lizihan021/Marty-the-robot/pic/marty/5.JPG

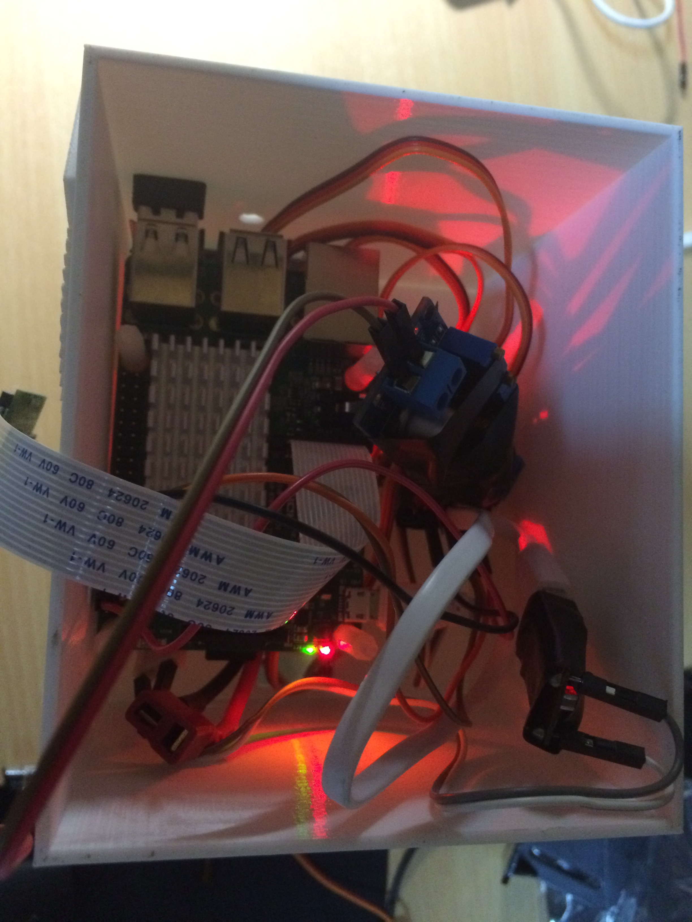
pic/marty/5.JPG
