lizihan021/Marty-the-robot/pic/marty/6.JPG

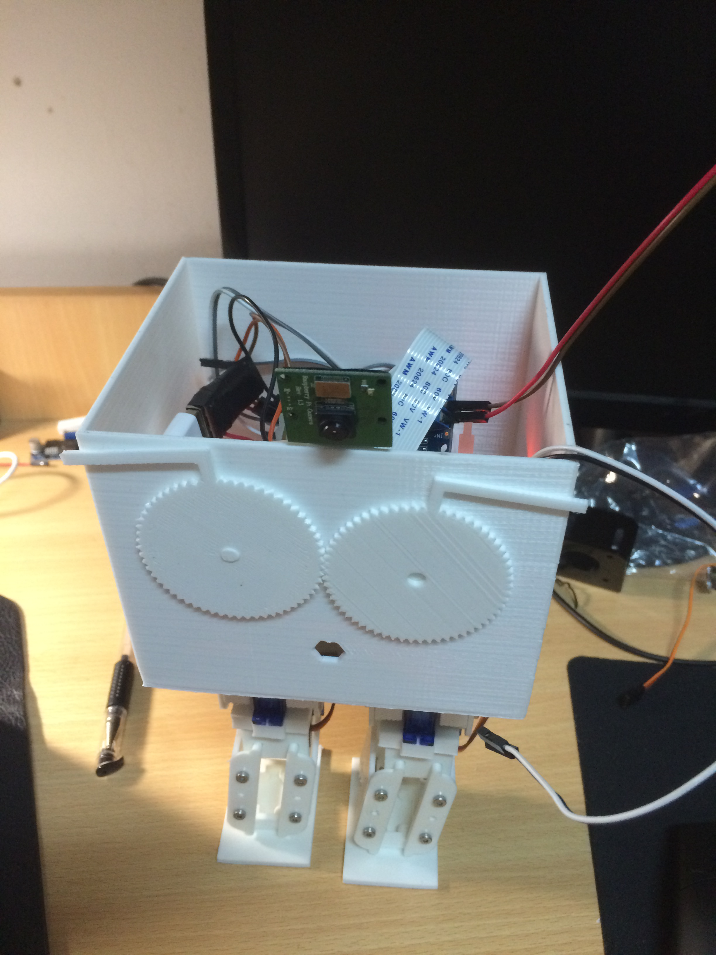
pic/marty/6.JPG
