lizihan021/Marty-the-robot/pic/marty/7.JPG

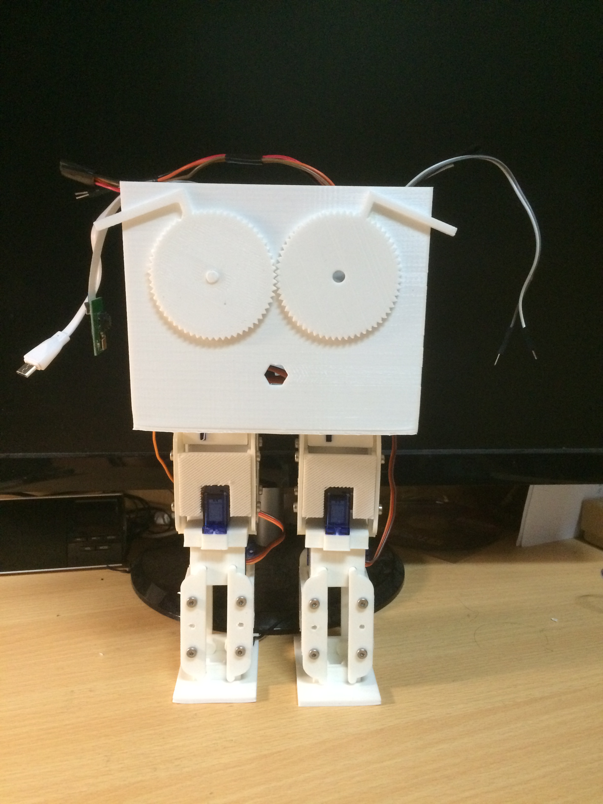
pic/marty/7.JPG
