lizihan021/Marty-the-robot/pic/marty/8.JPG

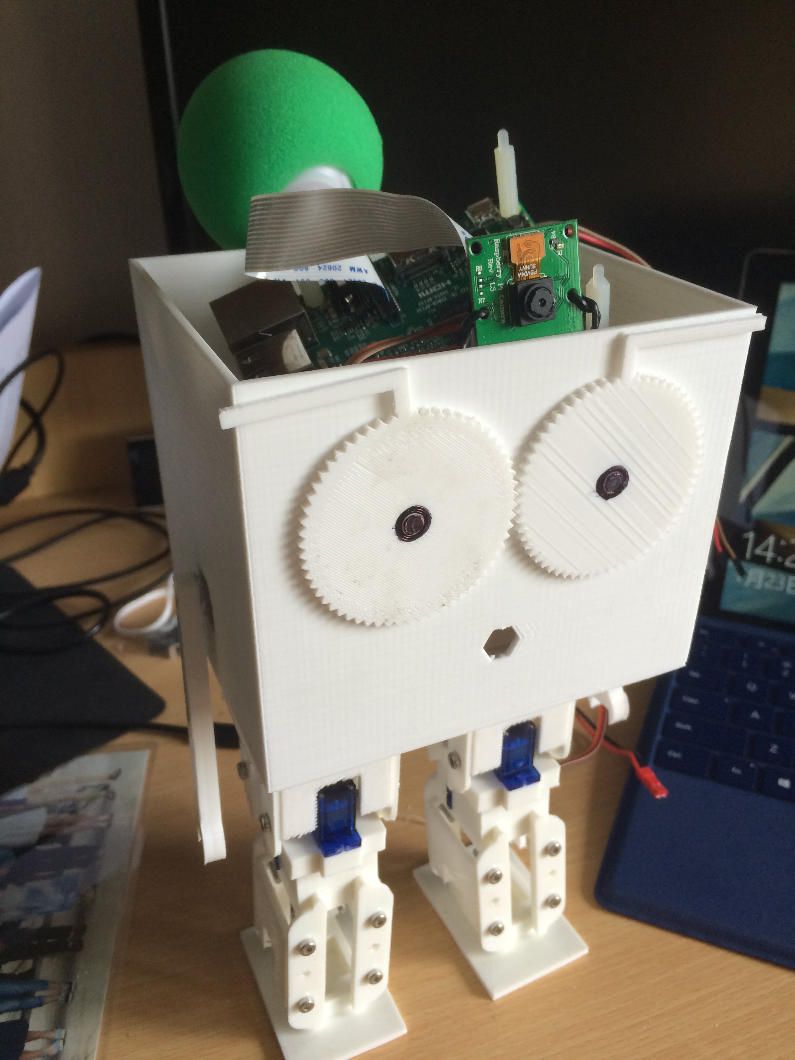
pic/marty/8.JPG
