lizihan021/Marty-the-robot/pic/marty/9.JPG

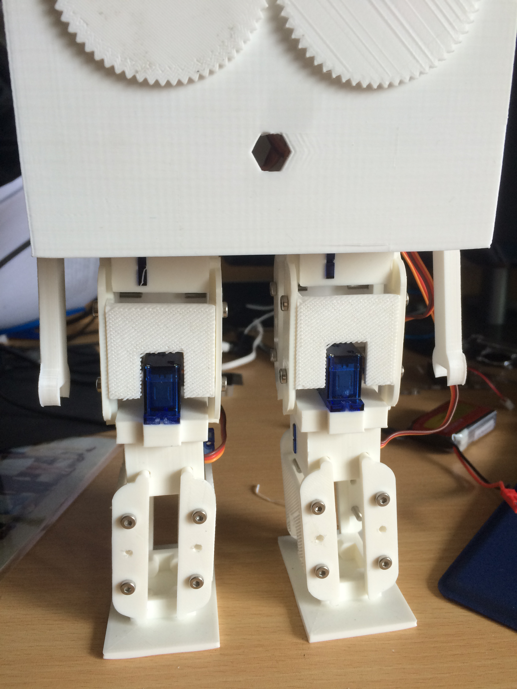
pic/marty/9.JPG
