lizihan021/Marty-the-robot/pic/marty/11.JPG

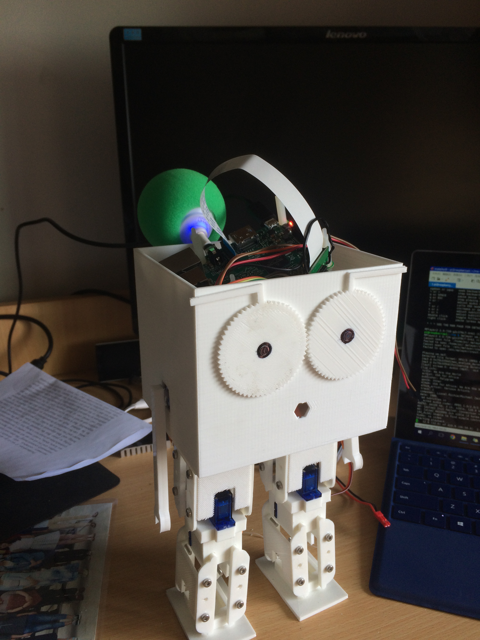
pic/marty/11.JPG
